rhardy24/Subaru-SSMII-DAQ/Subaru-SSMII-DAQ-T41-Ard/include/config.h

#include <Arduino.h>

#ifndef CONFIG__H_
#define CONFIG__H_

    /*************************************************************************
     * USER SETTINGS
    **************************************************************************/
    #define SERIAL_MONITOR_BAUD 115200

    //comment out following line to disable debug messages to USB Serial monitor
    #define DEBUG
    
#endif
